MarceAveni/alarma-y-domotica/Diseño y Hardware/Modelos 3D y Planos/Gabinete Frente/Base relés.stl

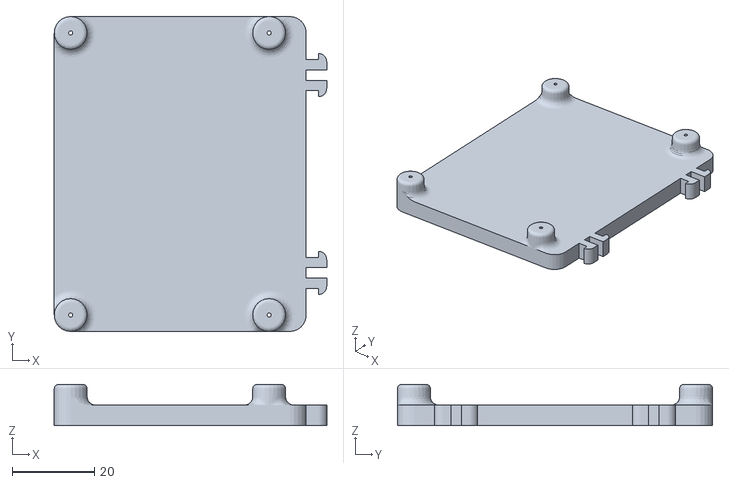
[picture p19: CAD file, 2026-06-27]
Diseño y Hardware/Modelos 3D y Planos/Gabinete Frente/Base relés.stl
66.3 x 76.6 x 10.00
