MarceAveni/alarma-y-domotica/Diseño y Hardware/Modelos 3D y Planos/Gabinete Frente/Carcasa sensor uW - C.stl

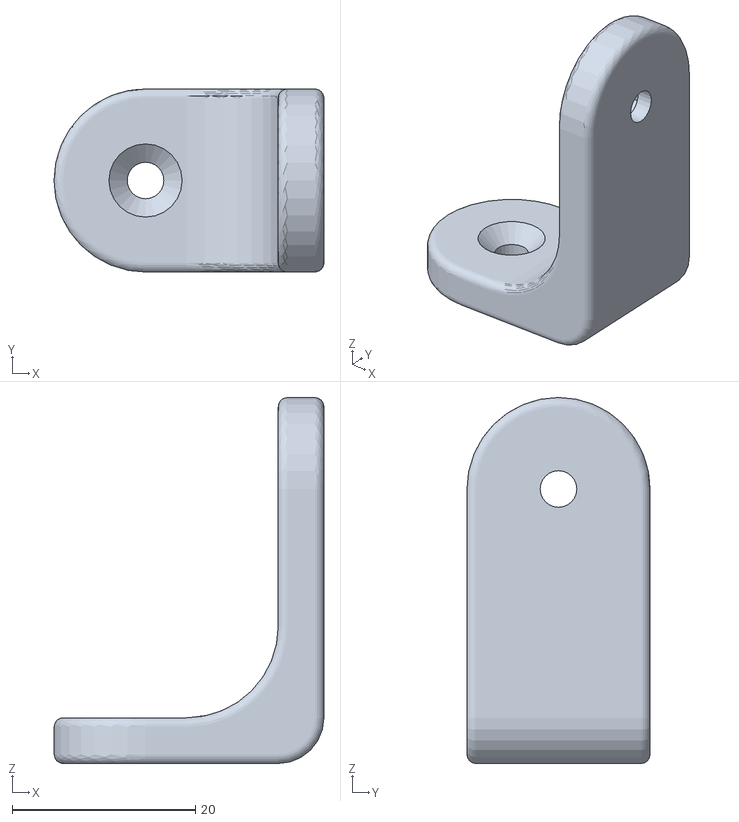
[picture p20: CAD file, 2026-06-27]
Diseño y Hardware/Modelos 3D y Planos/Gabinete Frente/Carcasa sensor uW - C.stl
29.5 x 20.0 x 40.0
