MarceAveni/alarma-y-domotica/Diseño y Hardware/Modelos 3D y Planos/Gabinete Frente/Base electrónica.stl

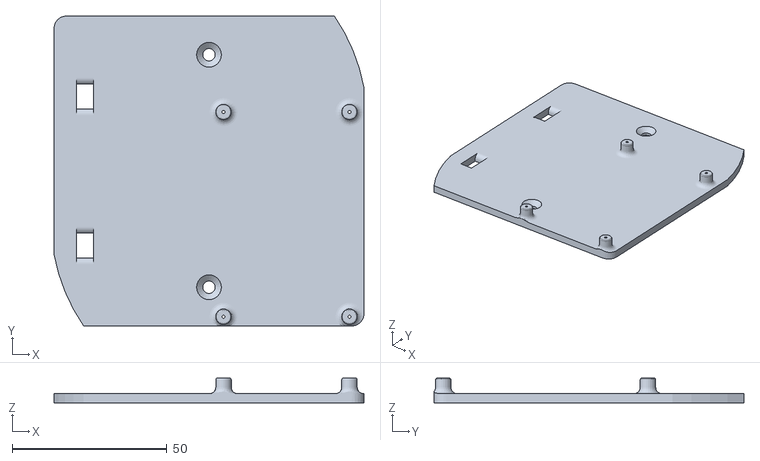
[picture p21: CAD file, 2026-06-27]
Diseño y Hardware/Modelos 3D y Planos/Gabinete Frente/Base electrónica.stl
100.0 x 100.0 x 8.00
